ojas-mediratta/BuzzCaster-Guitar/In-Progress Documentation/bracket1.png

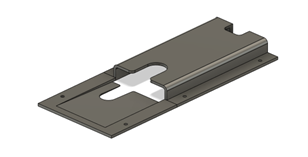
In-Progress Documentation/bracket1.png
